arisros/arkbutton-keyboard/cosmos/_block_parts.scad

// How the outer wall skin (chunk) relates to the MCU holder in the bay.
color([1,0.55,0.05]) import("case_chunk.stl");   // outer wall skin w/ connector openings
color([0.2,0.5,1])   import("holder.stl");         // RP2040-Zero + TRRS cradle
