arisros/arkbutton-keyboard/cosmos/_cm.scad

color([0.62,0.62,0.64]) import("case_main.stl");
