arisros/arkbutton-keyboard/cosmos/_main_only.scad

color([0.62,0.62,0.64]) import("case_main.stl");
