arisros/arkbutton-keyboard/cosmos/case_outline.scad

// AUTO-GENERATED by tools/gen-case-outline.mjs — do not edit by hand.
// Outer silhouette of cosmos/case_main.stl (manifold project, simplify 0.3 mm). 116 pts, area 15662 mm^2.
module case_outline() polygon(points=[[-35.04,-71.71],[-32.03,-68.87],[-29.67,-64.53],[-25.49,-54.33],[-27.08,-54.33],[-26.96,-53.43],[-17.64,-42.90],[-16.04,-39.78],[-15.59,-37.69],[-15.78,-35.74],[-17.27,-31.84],[-17.31,-30.54],[-15.49,-27.96],[-11.53,-26.33],[-2.50,-25.37],[0.56,-24.52],[2.05,-23.57],[3.30,-21.67],[3.27,-20.43],[-0.62,-13.63],[1.29,-12.18],[8.39,-12.19],[16.14,-13.61],[15.91,-14.80],[16.85,-16.01],[30.65,-17.28],[35.59,-17.05],[41.16,-15.70],[41.99,-14.98],[42.20,-14.09],[41.25,-10.40],[41.98,-9.67],[44.78,-8.80],[48.18,-8.56],[63.82,-9.42],[74.26,-11.14],[77.37,-11.21],[81.56,-9.93],[83.30,-8.44],[84.48,-6.60],[85.17,-4.34],[85.33,-1.43],[83.68,9.01],[83.22,53.83],[84.71,67.62],[84.42,70.16],[82.53,73.80],[80.83,75.20],[78.74,76.10],[76.15,76.49],[63.39,74.72],[60.62,74.72],[49.30,73.11],[45.31,73.10],[43.55,73.66],[41.96,74.93],[42.77,79.58],[44.17,82.28],[44.80,84.97],[44.09,86.58],[41.88,87.97],[38.21,88.71],[24.33,87.61],[19.83,87.66],[19.75,88.40],[18.84,88.82],[20.32,89.14],[19.97,89.38],[20.42,90.01],[15.46,90.73],[0.02,90.76],[-5.41,90.26],[-6.76,89.72],[-5.38,88.65],[-5.99,88.40],[-6.00,87.52],[-27.69,87.44],[-38.20,89.04],[-41.35,89.12],[-45.58,87.90],[-47.42,86.38],[-48.63,84.57],[-49.34,82.35],[-49.52,79.51],[-47.96,69.28],[-47.98,25.34],[-47.29,8.19],[-47.73,4.17],[-49.29,4.54],[-50.53,4.20],[-52.26,1.87],[-54.30,-8.45],[-56.34,-11.38],[-59.70,-14.94],[-66.07,-20.12],[-68.01,-22.26],[-69.35,-24.71],[-69.55,-26.87],[-68.72,-27.96],[-66.01,-29.58],[-65.41,-30.77],[-65.63,-32.38],[-67.39,-35.38],[-73.35,-40.73],[-75.65,-44.05],[-76.01,-45.79],[-75.52,-48.38],[-74.31,-50.53],[-72.47,-52.45],[-69.15,-54.73],[-56.36,-60.96],[-55.48,-60.08],[-53.09,-61.72],[-45.80,-69.51],[-43.06,-71.64],[-39.44,-72.77]]);
