arisros/arkbutton-keyboard/tools/tent/_asm.scad

color("RoyalBlue")  import("bottom.stl",convexity=5);
color("SteelBlue")  import("tenting-arm.stl",convexity=5);
color("Orange")     import("newplate_RIGHT.stl",convexity=10);
color("LightGray")  import("dep2/case.stl",convexity=5);
