arisros/arkbutton-keyboard/tools/tent/_asmchk.scad

import("bottom.stl", convexity=5);
import("tenting-arm.stl", convexity=5);
import("optionA_adapter.stl", convexity=5);
import("../assembled_optionA_case.stl", convexity=5);
color("red") import("mag/mag_kb.stl", convexity=5);
color("blue") import("mag/mag_tent.stl", convexity=5);
