arisros/arkbutton-keyboard/tools/tent/_basebot.scad

color("RoyalBlue") import("bottom.stl",convexity=6);
