arisros/arkbutton-keyboard/tools/tent/_cm.scad

color("SlateGray") import("cover_magfeet_RIGHT.stl",convexity=10);
