arisros/arkbutton-keyboard/tools/tent/_cmp.scad

translate([-110,0,0]) color("tan")    import("tentplate_RIGHT_orig.stl", convexity=6); // ORIGINAL repo plate
translate([ 110,0,0]) color("orange") import("cover_tent_RIGHT.stl", convexity=6);      // MY modified cover
