arisros/arkbutton-keyboard/tools/tent/_dep.scad

color("green")  import("bottom.stl", convexity=5);
color("orange") import("tenting-arm.stl", convexity=5);
color("tan")    import("rcb_right_orig.stl", convexity=5);
color("lightblue") import("dep/case.stl", convexity=5);
color("gray")   import("dep/cover.stl", convexity=5);
color("red")    import("dep/mag_kb.stl");
