arisros/arkbutton-keyboard/tools/tent/_flat2_cover.scad

rotate([-0.15,0,0]) rotate([0,-30.05,0]) import("final_cover_dl.stl", convexity=10);
