arisros/arkbutton-keyboard/tools/tent/_flat2_intb.scad

rotate([-0.15,0,0]) rotate([0,-30.05,0]) import("final_intbottom_dl.stl", convexity=10);
