arisros/arkbutton-keyboard/tools/tent/_flat_cover.scad

rotate([0,-30,0]) import("final_cover_dl.stl", convexity=10);
