arisros/arkbutton-keyboard/tools/tent/_flat_intb.scad

rotate([0,-30,0]) import("final_intbottom_dl.stl", convexity=10);
