arisros/arkbutton-keyboard/tools/tent/_kbonly.scad

color("LightGray")  import("dep2/case.stl", convexity=5);
color("DimGray")    import("dep2/cover.stl", convexity=5);
