arisros/arkbutton-keyboard/tools/tent/_kz.scad

color("Tomato") import("plate_solid_RIGHT_print.stl",convexity=12);
