arisros/arkbutton-keyboard/tools/tent/_mL.scad

mirror([1,0,0]) import("plate_mag_RIGHT.stl",convexity=10);
