arisros/arkbutton-keyboard/tools/tent/_mL2.scad

mirror([1,0,0]) import("cover_magfeet_RIGHT.stl",convexity=10);
