arisros/arkbutton-keyboard/tools/tent/_mLp.scad

mirror([1,0,0]) import("plate_mag_RIGHT_print.stl",convexity=10);
