arisros/arkbutton-keyboard/tools/tent/_orient2.scad

rotate(a=90,v=[-0.869,0.494,0]) import("plate_mag_RIGHT.stl",convexity=10);
