arisros/arkbutton-keyboard/tools/tent/_pb.scad

color("Orange") import("plate_mag_RIGHT_print.stl",convexity=10);
