arisros/arkbutton-keyboard/tools/tent/_pm.scad

color("Orange") import("plate_mag_RIGHT.stl",convexity=10);
