arisros/arkbutton-keyboard/tools/tent/_pmf.scad

rotate([22,0,0]) rotate([90,0,0]) rotate([0,0,-29.6]) color("Orange") import("plate_mag_RIGHT.stl",convexity=10);
