arisros/arkbutton-keyboard/tools/tent/_po.scad

color("Orange") import("plate_mag_RIGHT_print.stl",convexity=10);
