arisros/arkbutton-keyboard/tools/tent/_si.scad

color("Orange") import("plate_solid_RIGHT_print.stl",convexity=12);
