arisros/arkbutton-keyboard/tools/tent/_thole.scad

import("cover_tent_RIGHT.stl", convexity=5);
color("blue") import("mag/mag_tent_flat.stl");
