arisros/arkbutton-keyboard/tools/tent/_tp.scad

import("tentplate_RIGHT_orig.stl", convexity=10);
