arisros/arkbutton-keyboard/tools/tent/_v.scad

import("cover_magfeet_LEFT.stl",convexity=10);
